digixx/50hz_Monitor/software/ESP8266_50Hz_Monitor/credentials_template.h

// rename this file to credentials.h
//
// Wifi credentials
#define mySSID "Wifi"
#define myPASSWORD "secret"
#define mySonde "location-name"

// Server upload URL
#define myURL "http://my.server.com/upload.php"

// Complete HTTP request
// http://my.server.com/path/data.php?sonde=location2&freq=50.0118
